ConnerSanders/CapstoneStarterRepo/Documentation/Images/Electrolysis_System/CauxVoltage.jpg

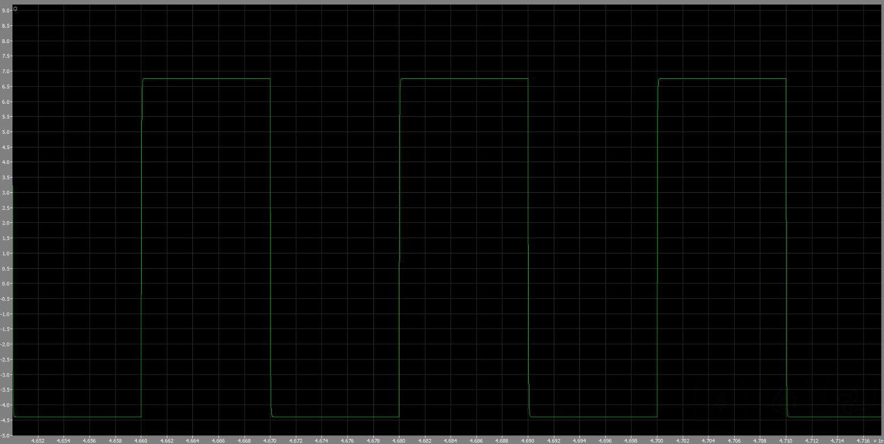
Documentation/Images/Electrolysis_System/CauxVoltage.jpg
