ConnerSanders/CapstoneStarterRepo/Documentation/Images/Electrolysis_System/loadVoltage.jpg

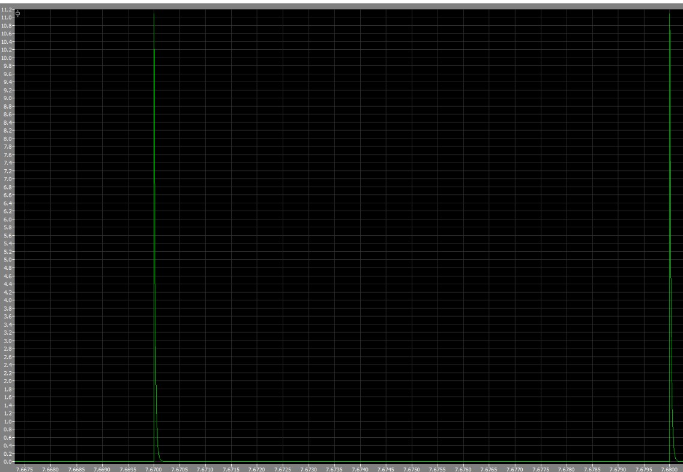
Documentation/Images/Electrolysis_System/loadVoltage.jpg
