ConnerSanders/CapstoneStarterRepo/Documentation/Images/Electrolysis_System/PLECS_Simulation.jpg

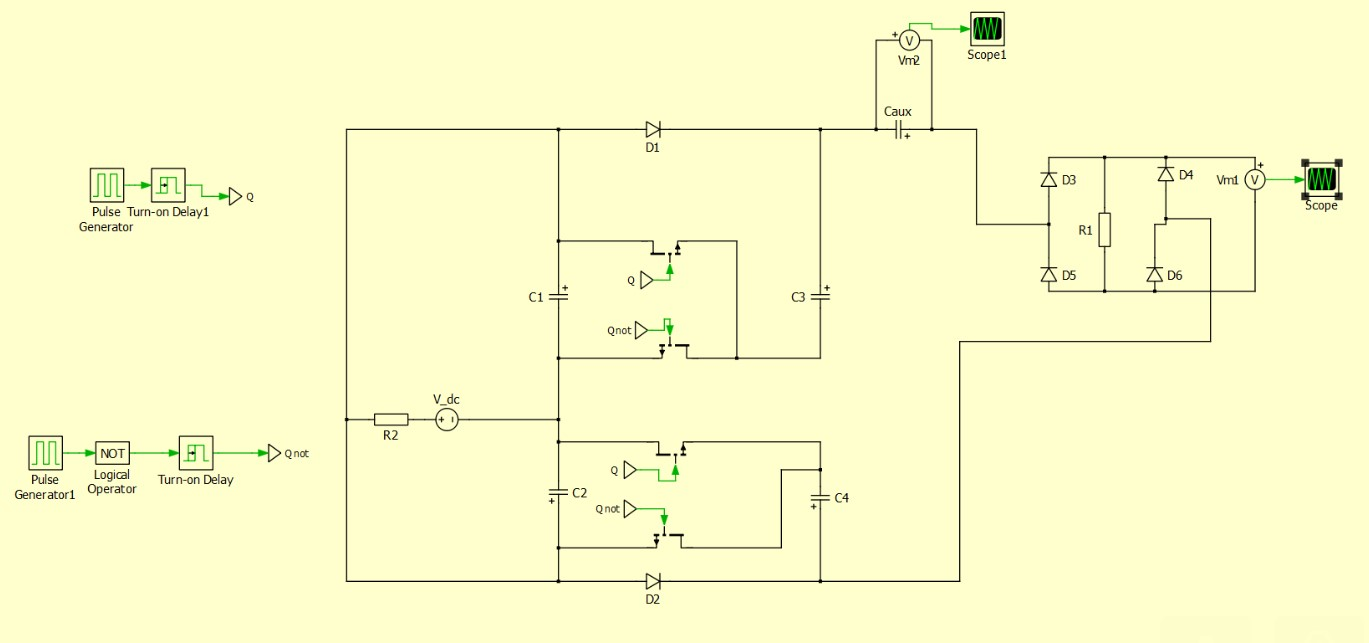
Documentation/Images/Electrolysis_System/PLECS_Simulation.jpg
